maugsburger/rfdht22/master_sheet2.png

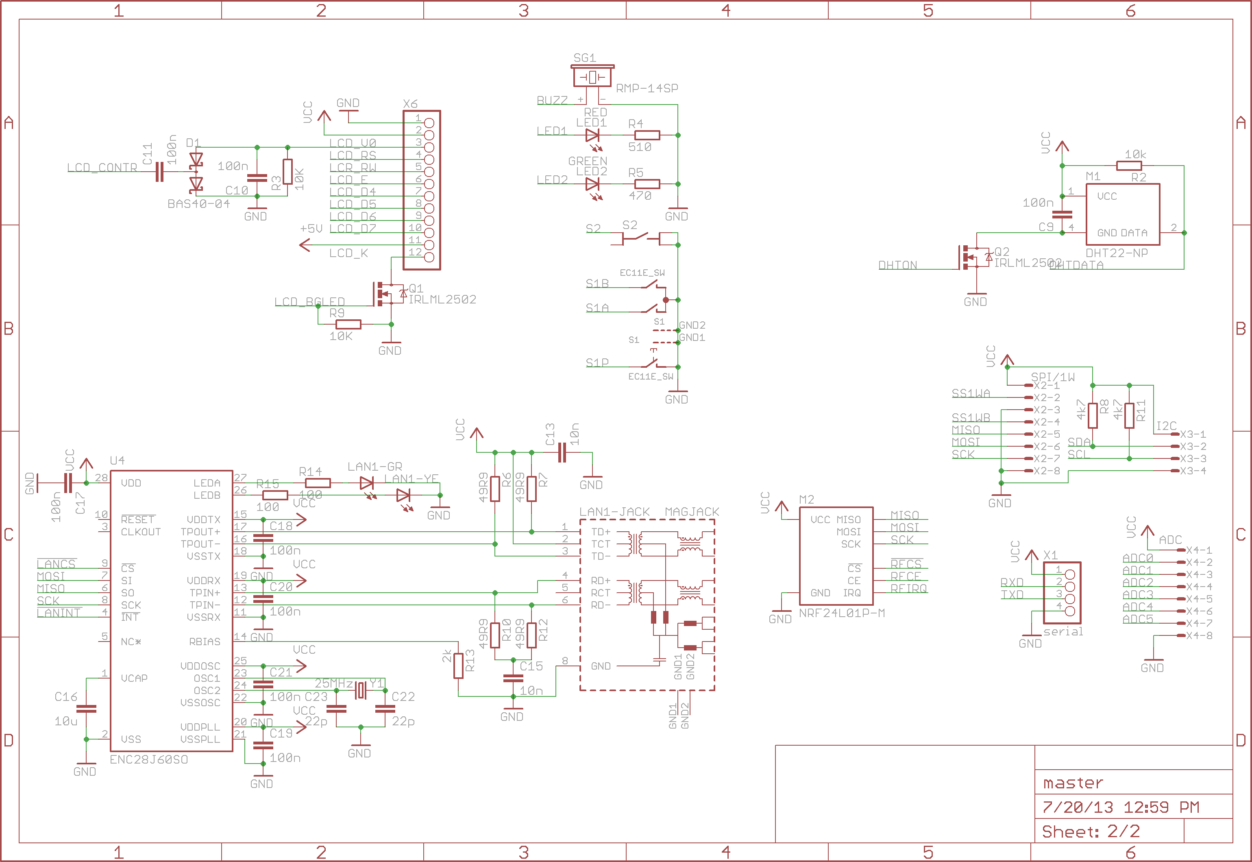
master_sheet2.png
