maugsburger/rfdht22/master_top.png

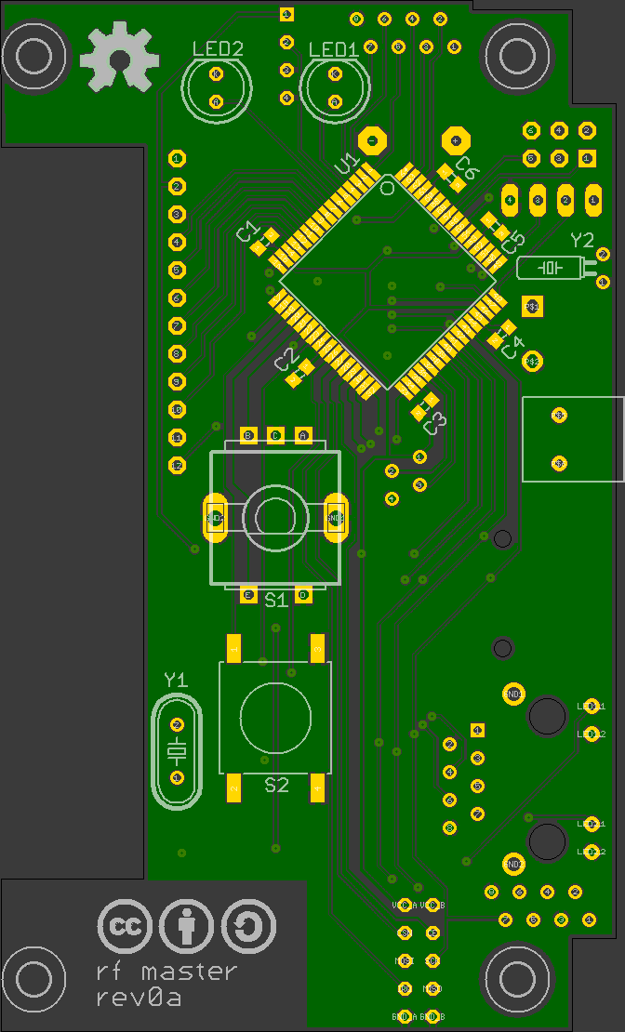
master_top.png
