maugsburger/rfdht22/sensor-tiny2313a_sheet1.png

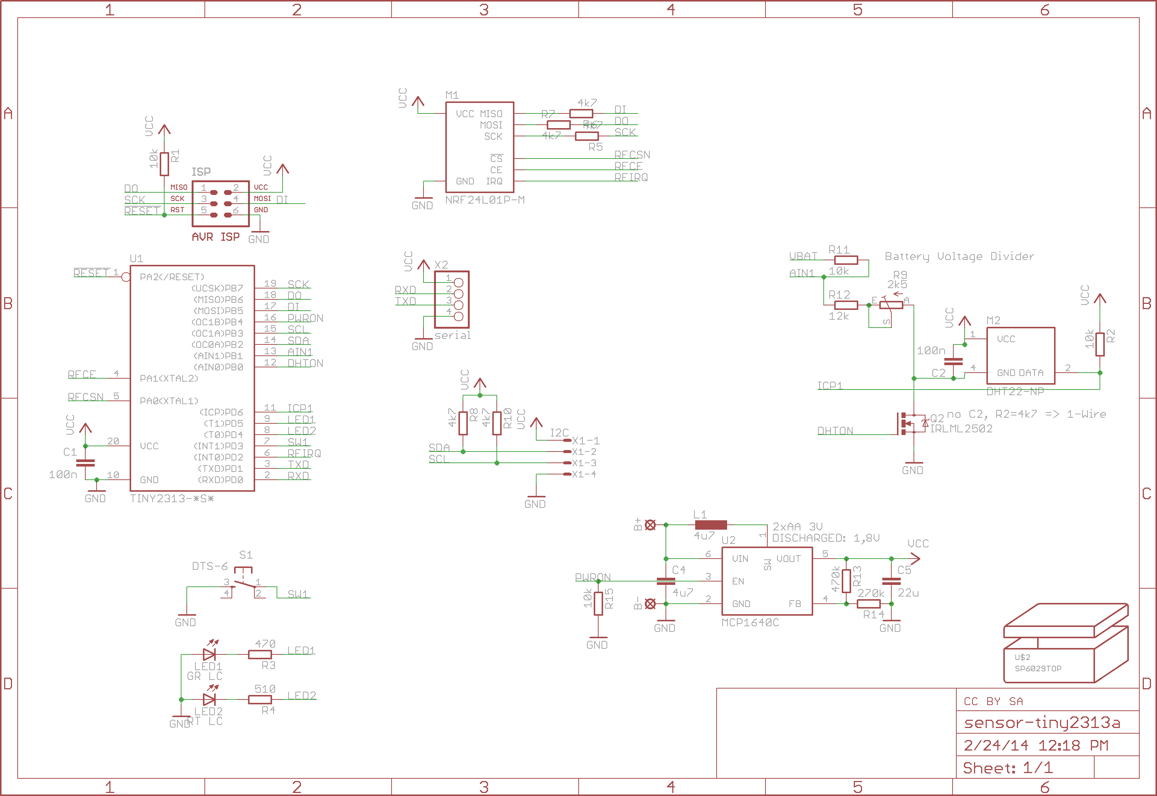
sensor-tiny2313a_sheet1.png
