maugsburger/rfdht22/sensor-xmegab3_top.png

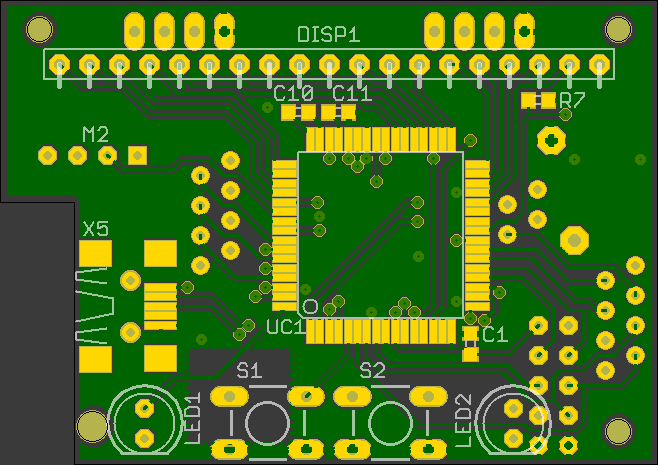
sensor-xmegab3_top.png
